fluorumlabs/sonictrain-old/a405-diode-distortion.brd

## EAGLE design a405-diode-distortion.brd (2016-03-17)

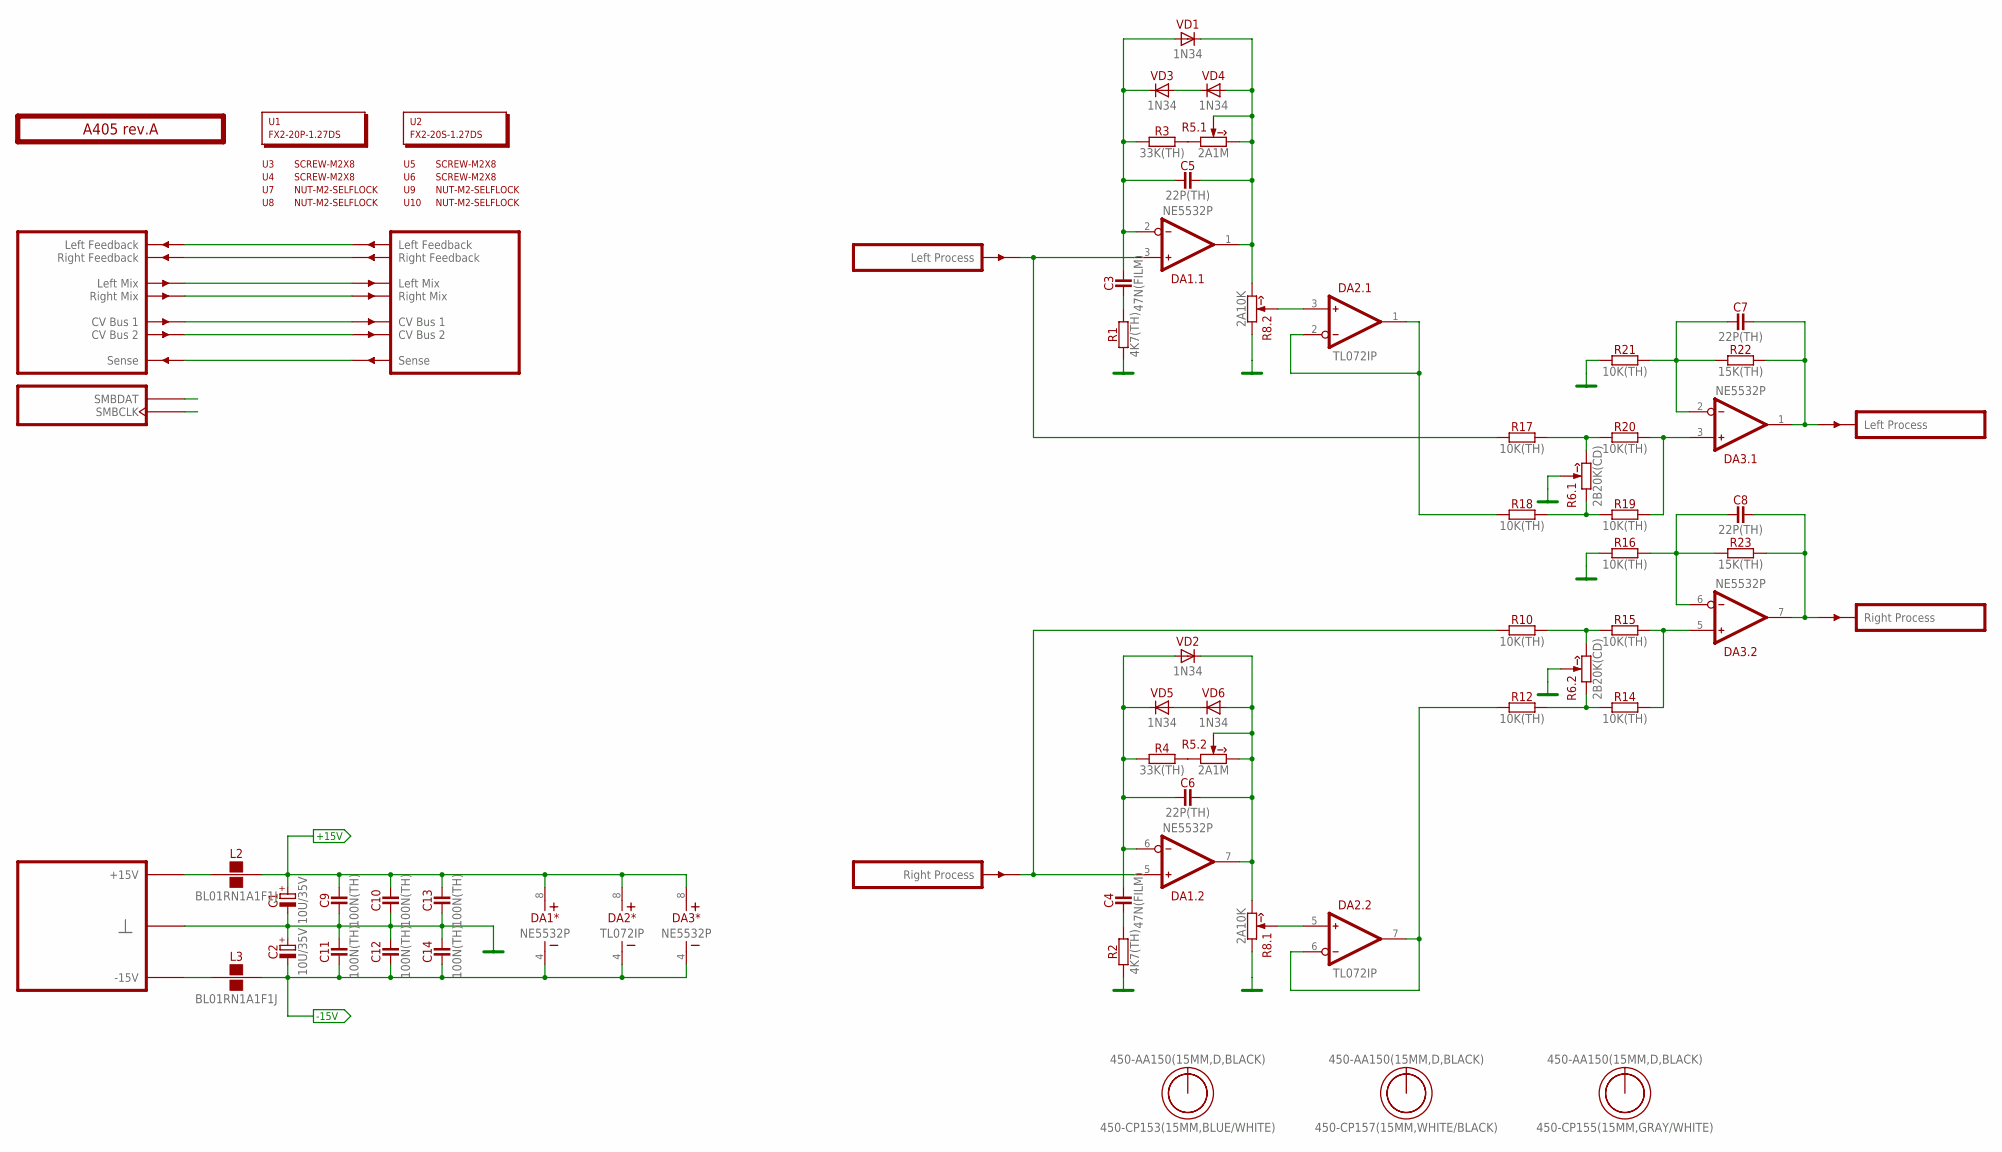
[picture p34: schematic a405-diode-distortion.sch]

Parts:
C1, C2: 10U/35V; E2-5
C3, C4: 47N(FILM); C050-025X075
C5, C6, C7, C8: 22P(TH); C050-024X044
C9, C10, C11, C12, C13, C14: 100N(TH); C050-024X044
DA1, DA3: NE5532P; DIP-8
DA2: TL072IP; DIP-8
L2, L3: BL01RN1A1F1J; BL01RN1A
O2, O3, O4: 450-AA150(15MM,D,BLACK); EMPTY
O5: 450-CP155(15MM,GRAY/WHITE); EMPTY
O6: 450-CP157(15MM,WHITE/BLACK); EMPTY
O7: 450-CP153(15MM,BLUE/WHITE); EMPTY
PCB1: A405 rev.A; ST2-BOARD-50
R1, R2: 4K7(TH); R-0207/10
R3, R4: 33K(TH); R-0207/10
R5: 2A1M; RV11-DUAL
R6: 2B20K(CD); RV11-DUAL
R8: 2A10K; RV11-DUAL
R10, R12, R14, R15, R16, R17, R18, R19, R20, R21: 10K(TH); R-0207/10
R22, R23: 15K(TH); R-0207/10
U1: FX2-20P-1.27DS; EMPTY
U2: FX2-20S-1.27DS; EMPTY
U3, U4, U5, U6: SCREW-M2X8; EMPTY
U7, U8, U9, U10: NUT-M2-SELFLOCK; EMPTY
VD1, VD2, VD3, VD4, VD5, VD6: 1N34; DO35-15

Connections:
+15V: C1.+, C9.2, C10.2, C13.2, DA1.8 (V+), DA2.8 (V+), DA3.8 (V+), L2.2
-15V: C2.-, C11.1, C12.1, C14.1, DA1.4 (V-), DA2.4 (V-), DA3.4 (V-), L3.2
FBK_LEFT: PCB1.ALFBK (LFBK), PCB1.ALFBK' (LFBK')
FBK_RIGHT: PCB1.ARFBK (RFBK), PCB1.ARFBK' (RFBK')
GND: C1.-, C2.+, C9.1, C10.1, C11.2, C12.2, C13.1, C14.2, PCB1.B4 (GND), PCB1.B4' (GND), PCB1.B5 (GND), PCB1.B5' (GND), PCB1.B6 (GND), PCB1.B6' (GND), PCB1.B7 (GND), PCB1.B7' (GND), PCB1.B8 (GND), PCB1.B8' (GND), R1.1, R2.1, R6.2 (W), R6.2' (W), R8.1 (CCW), R8.1' (CCW), R16.1, R21.1
LMIX: PCB1.ALMIX (LMIX), PCB1.ALMIX' (LMIX')
unnamed: R3.2, R5.1 (CCW)
unnamed: R4.2, R5.1' (CCW)
unnamed: C7.2, DA3.1 (OUT), PCB1.BOUTL' (OUTL), R22.2
unnamed: C3.1, R1.2
unnamed: R6.3 (CW), R17.2, R20.1
unnamed: DA1.5 (IN+), PCB1.BINR (INR), R10.1
unnamed: C6.2, DA1.7 (OUT), R5.2' (W), R5.3' (CW), R8.3 (CW), VD2.C, VD6.A
unnamed: C4.1, R2.2
unnamed: C5.2, DA1.1 (OUT), R5.2 (W), R5.3 (CW), R8.3' (CW), VD1.C, VD4.A
unnamed: C4.2, C6.1, DA1.6 (IN-), R4.1, VD2.A, VD5.C
unnamed: C8.1, DA3.6 (IN-), R16.2, R23.1
unnamed: DA3.5 (IN+), R14.2, R15.2
unnamed: DA3.3 (IN+), R19.2, R20.2
unnamed: VD3.A, VD4.C
unnamed: R6.1' (CCW), R12.2, R14.1
unnamed: PCB1.BSENSE (SENSE), PCB1.BSENSE' (SENSE')
unnamed: C3.2, C5.1, DA1.2 (IN-), R3.1, VD1.A, VD3.C
unnamed: DA1.3 (IN+), PCB1.BINL (INL), R17.1
unnamed: C8.2, DA3.7 (OUT), PCB1.BOUTR' (OUTR), R23.2
unnamed: VD5.A, VD6.C
unnamed: DA2.5 (IN+), R8.2 (W)
unnamed: DA2.6 (IN-), DA2.7 (OUT), R12.1
unnamed: DA2.3 (IN+), R8.2' (W)
unnamed: DA2.1 (OUT), DA2.2 (IN-), R18.1
unnamed: L3.1, PCB1.A-15 (P-15V), PCB1.A-15' (P-15V), PCB1.B-15 (P-15V), PCB1.B-15' (P-15V)
unnamed: PCB1.ASMBDAT (SMBDAT), PCB1.ASMBDAT' (SMBDAT)
unnamed: PCB1.ACV1 (CV1), PCB1.ACV1' (CV1')
unnamed: PCB1.ACV2 (CV2), PCB1.ACV2' (CV2')
unnamed: PCB1.ASMBCLK (SMBCLK), PCB1.ASMBCLK' (SMBCLK)
unnamed: R6.1 (CCW), R18.2, R19.1
unnamed: R6.3' (CW), R10.2, R15.1
unnamed: C7.1, DA3.2 (IN-), R21.2, R22.1
P+15V: L2.1, PCB1.A+15 (P+15V), PCB1.A+15' (P+15V), PCB1.B+15 (P+15V), PCB1.B+15' (P+15V)
RMIX: PCB1.ARMIX (RMIX), PCB1.ARMIX' (RMIX')

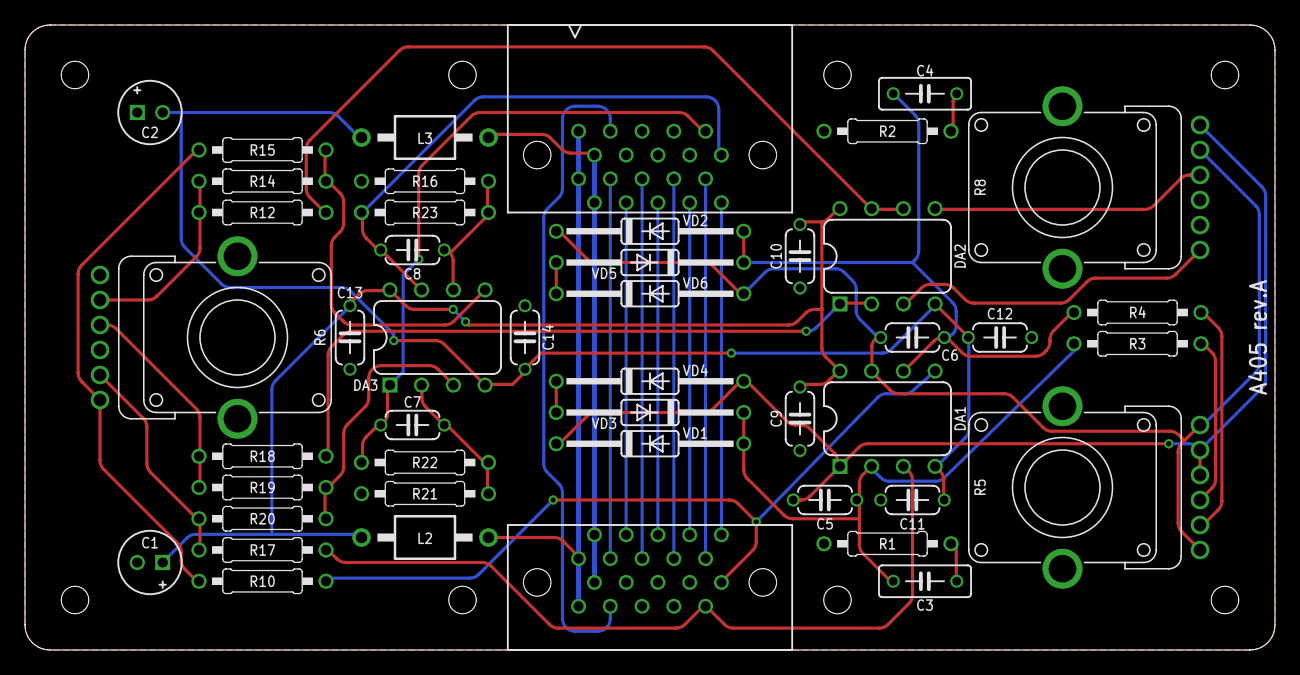
[picture p35: board a405-diode-distortion.brd from above]

Board: 2 copper layers, 100.0 x 50.0 mm, 61 parts (0 on the bottom side), 40 nets.
