fluorumlabs/sonictrain-old/m202-stereo-input.brd

## EAGLE design m202-stereo-input.brd (2016-03-17)

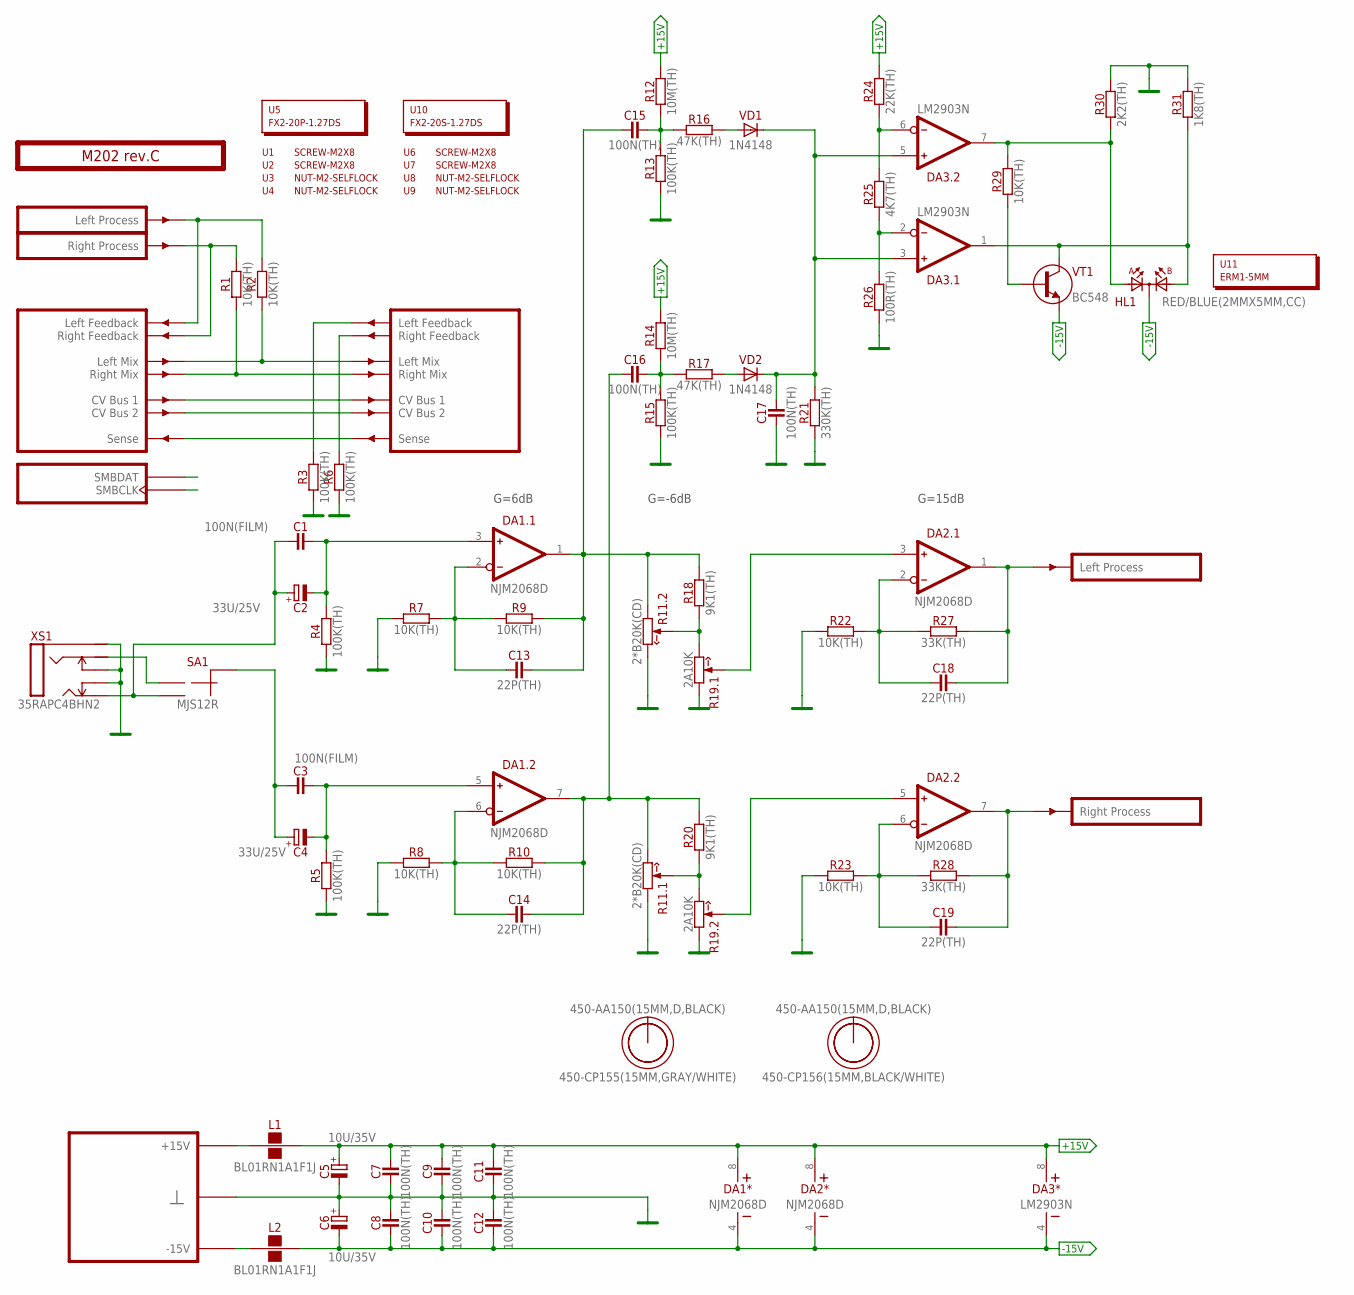
[picture p36: schematic m202-stereo-input.sch]

Parts:
C1, C3: 100N(FILM); C050-025X075
C2, C4: 33U/25V; E2,5-7
C5, C6: 10U/35V; E2-5
C7, C8, C9, C10, C11, C12, C15, C16, C17: 100N(TH); C050-024X044
C13, C14, C18, C19: 22P(TH); C050-024X044
DA1, DA2: NJM2068D; DIP-8
DA3: LM2903N; DIP-8
HL1: RED/BLUE(2MMX5MM,CC); LED2X5-3PIN
L1, L2: BL01RN1A1F1J; BL01RN1A
O1, O3: 450-AA150(15MM,D,BLACK); EMPTY
O2: 450-CP155(15MM,GRAY/WHITE); EMPTY
O4: 450-CP156(15MM,BLACK/WHITE); EMPTY
PCB1: M202 rev.C; ST2-BOARD-50
R1, R2, R7, R8, R9, R10, R22, R23, R29: 10K(TH); R-0207/10
R3, R4, R5, R6, R13, R15: 100K(TH); R-0207/10
R11: 2*B20K(CD); RV11-DUAL
R12, R14: 10M(TH); R-0207/10
R16, R17: 47K(TH); R-0207/10
R18, R20: 9K1(TH); R-0207/10
R19: 2A10K; RV11-DUAL
R21: 330K(TH); R-0207/10
R24: 22K(TH); R-0207/10
R25: 4K7(TH); R-0207/10
R26: 100R(TH); R-0207/10
R27, R28: 33K(TH); R-0207/10
R30: 2K2(TH); R-0207/10
R31: 1K8(TH); R-0207/10
SA1: MJS12R; APEM-MJS12R
U1, U2, U6, U7: SCREW-M2X8; EMPTY
U3, U4, U8, U9: NUT-M2-SELFLOCK; EMPTY
U5: FX2-20P-1.27DS; EMPTY
U10: FX2-20S-1.27DS; EMPTY
U11: ERM1-5MM; EMPTY
VD1, VD2: 1N4148; DO35-7
VT1: BC548; TO92
XS1: 35RAPC4BHN2; 35RAP

Connections:
+15V: C5.+, C7.2, C9.2, C11.2, DA1.8 (V+), DA2.8 (V+), DA3.8 (V+), L1.2, R12.2, R14.2, R24.2
-15V: C6.-, C8.1, C10.1, C12.1, DA1.4 (V-), DA2.4 (V-), DA3.4 (V-), HL1.K, L2.2, VT1.3 (E)
GND: C5.-, C6.+, C7.1, C8.2, C9.1, C10.2, C11.1, C12.2, C17.1, PCB1.B4 (GND), PCB1.B4' (GND), PCB1.B5 (GND), PCB1.B5' (GND), PCB1.B6 (GND), PCB1.B6' (GND), PCB1.B7 (GND), PCB1.B7' (GND), PCB1.B8 (GND), PCB1.B8' (GND), R3.1, R4.1, R5.1, R6.1, R7.1, R8.1, R11.1 (CCW), R11.3' (CW), R13.1, R15.1, R19.1 (CCW), R19.1' (CCW), R21.1, R22.1, R23.1, R26.1, R30.2, R31.2, XS1.1 (S), XS1.10 (TN), XS1.11 (RN)
LMIX: PCB1.ALMIX (LMIX), PCB1.ALMIX' (LMIX'), R2.1
unnamed: L1.1, PCB1.A+15 (P+15V), PCB1.A+15' (P+15V), PCB1.B+15 (P+15V), PCB1.B+15' (P+15V)
unnamed: PCB1.ARFBK' (RFBK'), R6.2
unnamed: DA2.3 (IN+), R19.2 (W)
unnamed: PCB1.ALFBK' (LFBK'), R3.2
unnamed: L2.1, PCB1.A-15 (P-15V), PCB1.A-15' (P-15V), PCB1.B-15 (P-15V), PCB1.B-15' (P-15V)
unnamed: SA1.NC (1), XS1.3 (R)
unnamed: C1.1, C2.+, SA1.NO (2), XS1.2 (T)
unnamed: DA2.5 (IN+), R19.2' (W)
unnamed: C3.2, C4.-, DA1.5 (IN+), R5.2
unnamed: C1.2, C2.-, DA1.3 (IN+), R4.2
unnamed: C19.2, DA2.7 (OUT), PCB1.BOUTR' (OUTR), R28.2
unnamed: C18.2, DA2.1 (OUT), PCB1.BOUTL' (OUTL), R27.2
unnamed: C18.1, DA2.2 (IN-), R22.2, R27.1
unnamed: C19.1, DA2.6 (IN-), R23.2, R28.1
unnamed: C14.2, C16.1, DA1.7 (OUT), R10.2, R11.3 (CW), R20.2
unnamed: PCB1.BSENSE (SENSE), PCB1.BSENSE' (SENSE')
unnamed: C15.2, R12.1, R13.2, R16.1
unnamed: C13.2, C15.1, DA1.1 (OUT), R9.2, R11.1' (CCW), R18.2
unnamed: C13.1, DA1.2 (IN-), R7.2, R9.1
unnamed: C14.1, DA1.6 (IN-), R8.2, R10.1
unnamed: R16.2, VD1.A
unnamed: R11.2' (W), R18.1, R19.3 (CW)
unnamed: C16.2, R14.1, R15.2, R17.1
unnamed: R11.2 (W), R19.3' (CW), R20.1
unnamed: C3.1, C4.+, SA1.C (CM)
unnamed: PCB1.ASMBDAT (SMBDAT), PCB1.ASMBDAT' (SMBDAT)
unnamed: PCB1.ARFBK (RFBK), PCB1.BINR (INR), R1.2
unnamed: PCB1.ALFBK (LFBK), PCB1.BINL (INL), R2.2
unnamed: PCB1.ACV1 (CV1), PCB1.ACV1' (CV1')
unnamed: PCB1.ACV2 (CV2), PCB1.ACV2' (CV2')
unnamed: PCB1.ASMBCLK (SMBCLK), PCB1.ASMBCLK' (SMBCLK)
unnamed: R17.2, VD2.A
unnamed: C17.2, DA3.3 (IN+), DA3.5 (IN+), R21.2, VD1.C, VD2.C
unnamed: DA3.2 (IN-), R25.1, R26.2
unnamed: DA3.6 (IN-), R24.1, R25.2
unnamed: DA3.7 (OUT), HL1.A1, R29.2, R30.1
unnamed: R29.1, VT1.2 (B)
unnamed: DA3.1 (OUT), HL1.A2, R31.1, VT1.1 (C)
RMIX: PCB1.ARMIX (RMIX), PCB1.ARMIX' (RMIX'), R1.1

Notes on the sheet:
G=6dB
G=-6dB
G=15dB
