fluorumlabs/sonictrain-old/m202-stereo-input.brd

## EAGLE design m202-stereo-input.brd (continued)

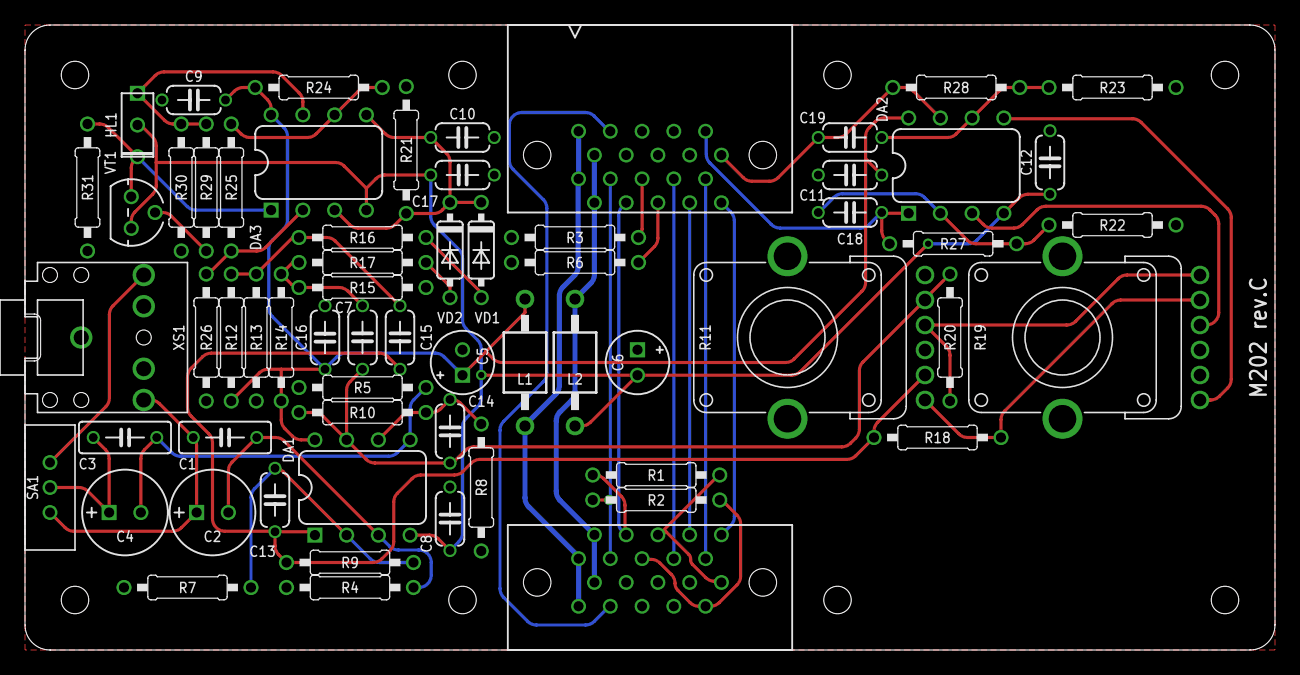
[picture p37: board m202-stereo-input.brd from above]

Board: 2 copper layers, 100.0 x 50.0 mm, 77 parts (0 on the bottom side), 43 nets.
